iOsnaaente/Tracker/3D/models/celula.jpg

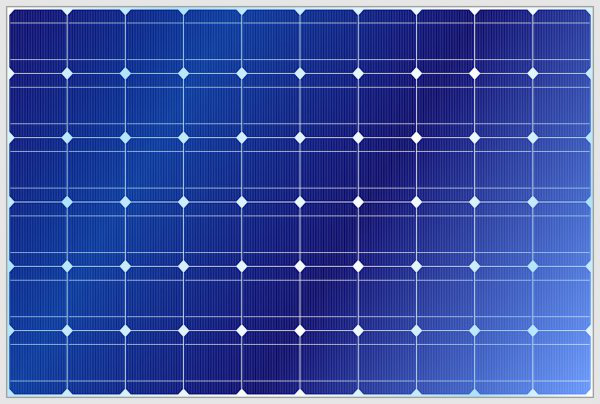
3D/models/celula.jpg
