iOsnaaente/Tracker/3D/models/Eixo_sf.png

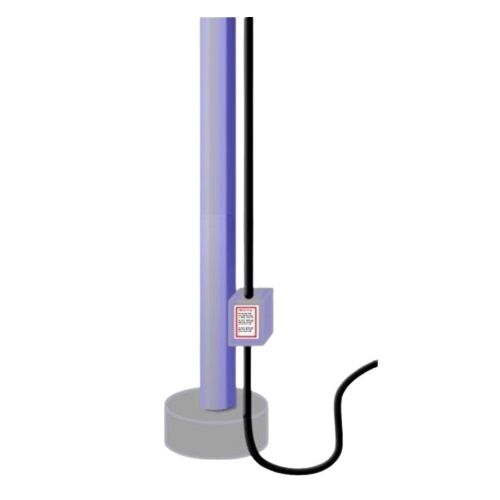
3D/models/Eixo_sf.png
