iOsnaaente/Tracker/Pico-Back/Rasp-pico-02-03-22/Tracker/Sensor/myAS5600.py

import machine 
import time 

MD_CHECK = 1
MH_CHECK = 2
ML_CHECK = 3 

class AS5600: 
  ##  FIGURE 21 - DATASHEET available in https://ams.com/documents/20143/36005/AS5600_DS000365_5-00.pdf
  ## Configuration registers 
  ZMCO      = 0x0 
  ZPOS      = 0x1
  MPOS      = 0x3
  MANG      = 0x5
  CONF      = 0x7
  ## Output Registers
  RAWANGLE  = 0x0C
  ANGLE     = 0x0E
  ## Status Registers
  STATUS    = 0x0B
  AGC       = 0x1A
  MAGNITUDE = 0x1B 
  ## Burn Commands 
  BURN      = 0xff

  # Magnetic sensor stuffs 
  Status     = 0       # Status register (MD, ML, MH)
  ADDRESS    = 0x36    # By default 

  startAngle = 0  # starting angle
  totalAngle = 0  # total absolute angular displacement
  
  ## Constructor 
  def __init__( self, I2C : machine.I2C , addr : int = 0x36, startAngle : float = 0.0  ): 
    self.ADDRESS    = addr 
    self.AS5600     = I2C 
    self.startAngle = startAngle
    self.LAST_ANGLE = startAngle
    self.ERRORS     = 0 
    
  def set_config( self ):
    for i in range( 9 ):
        try: 
            self._write( i, chr(0) )
        except:
            self.ERRORS += 1 
            print( 'Erro de configuração addr:{}'.format(i))

  ## To write in the I2C we need a buffer struct like b'a21@\x02' 
  def _write( self, addr_mem : int, buffer : bytes ) -> None:
    try:
        if type( self.AS5600 ) == machine.I2C: 
          self.AS5600.writeto_mem( self.ADDRESS, addr_mem, buffer )
        elif type( self.AS5600 ) == machine.SoftI2C:
          self.AS5600.writeto( self.ADDRESS, buffer, addr_mem )
    except:
        self.ERRORS += 1 
        #print( "AS5600 - ERROR -> _write line 49 ")
        pass
    
  ## to read, we start at addr_mem and we read num_bytes from addr_mem 
  def _read( self, addr_mem : int, num_bytes : int = 2 ) -> list:
    try:
        if type( self.AS5600 ) == machine.I2C: 
          return self.AS5600.readfrom_mem( self.ADDRESS, addr_mem, num_bytes )
        elif type( self.AS5600 ) == machine.SoftI2C:
          return self.AS5600.readfrom( self.ADDRESS, num_bytes, addr_mem )
    except:
        self.ERRORS += 1 
        #print( "AS5600 - ERROR -> _read line 60 ")
        pass 

  ## read the unscaled angle and unmodified angle
  def rawAngle( self ) -> bytes:
    try:
        raw_angle = self._read( self.ANGLE, 2 )
        HIGH_BYTE = raw_angle[0]    #  RAW ANGLE(11:8) on 0x0C address 
        LOW_BYTE  = raw_angle[1]    #  RAW ANGLE(7:0) on 0X0D address 
        RAW_ANGLE = ( (HIGH_BYTE << 8) | LOW_BYTE ) 
        return RAW_ANGLE 
    except: 
        self.ERRORS += 1
        if self.ERRORS > 10:
            self.set_config()
        return -1  

  def gain(self):
    self.GAIN = self._read( self.AGC , 1 )
    return self.GAIN

  ## Read the scaled angle 
  def degAngle( self ) -> bytes : 
    # To calculate the real angle : 
    # We have to divide the 360º by the 12bits (0x0fff) plus the value from the sensor
    # rawAngle * 360/4096 = rawAngle * 0.087890625
    RAW_ANGLE = self.rawAngle()
    if RAW_ANGLE == -1: DEG_ANGLE = self.LAST_ANGLE 
    else:               DEG_ANGLE = RAW_ANGLE * ( 360.0 / 0x0fff )
    self.LAST_ANGLE = (DEG_ANGLE - self.startAngle) if (DEG_ANGLE - self.startAngle) >= 0 else (DEG_ANGLE - self.startAngle)+360
    
    # If the angle is negative, we have to normalize it to be between [0, 360)º
    return self.LAST_ANGLE
    

  ## Verify the status of the magnetic range 
  ### The status be in the 0x0B address in the 5:3 bits
  #  
  ## MH [3] AGC minimum gain overflow, magnet too strong  
  ## ML [4] AGC maximum gain overflow, magnet too weak
  ## MD [5] Magnet was detected
  #
  ## To operate properly, the MD have to be set and the MH and ML have to be 0 
  def checkStatus( self ): 
    status = self._read( self.STATUS, 1 )
    self.MH = status[0] >> 3 and 1
    self.ML = status[0] >> 4 and 1
    self.MD = status[0] >> 5 and 1

    ## Return 0 if OK, else -1 to low magnetic level or 1 to high magnetic level 
    if self.MD:
      return MD_CHECK
    else: 
      if self.MH:
        return MH_CHECK
      if self.ML:
        return  ML_CHECK

    def diagnosis(self):
        print( self._read( 0, 11 ) )

    def get_ack( self ):
        return self.ERRORS 
